Acliad/Ahsokas-Lightsaber/Reference Images/View 2.png

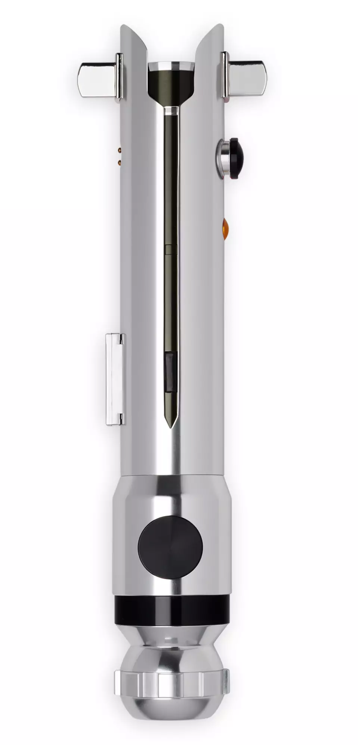
Reference Images/View 2.png
