Acliad/Ahsokas-Lightsaber/Mechanical/Meshes/Wing.stl

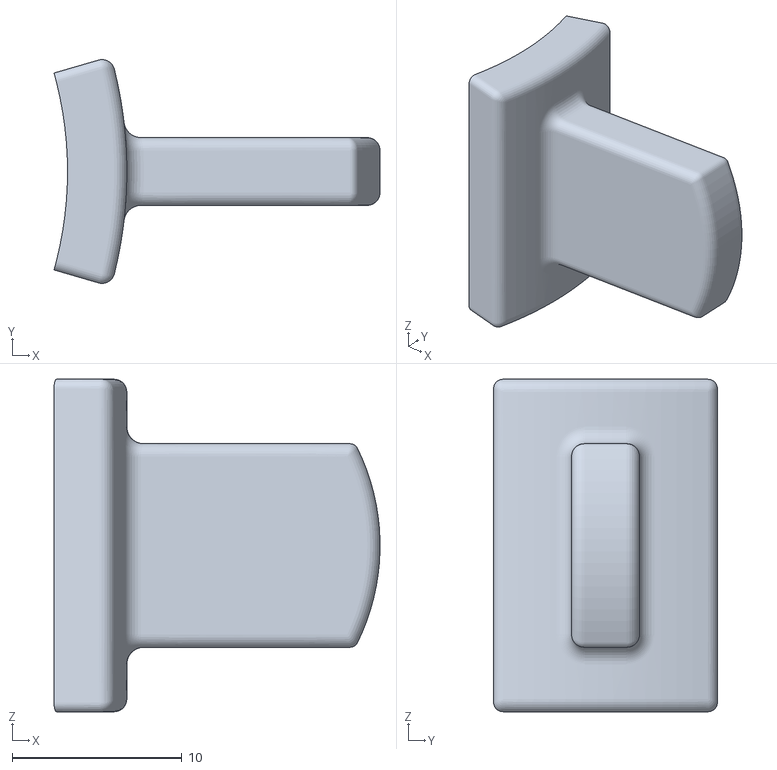
[picture p18: CAD file, 2024-09-22]
Mechanical/Meshes/Wing.stl
19.2 x 13.2 x 19.6
