Acliad/Ahsokas-Lightsaber/Mechanical/Meshes/Power Button Cap.stl

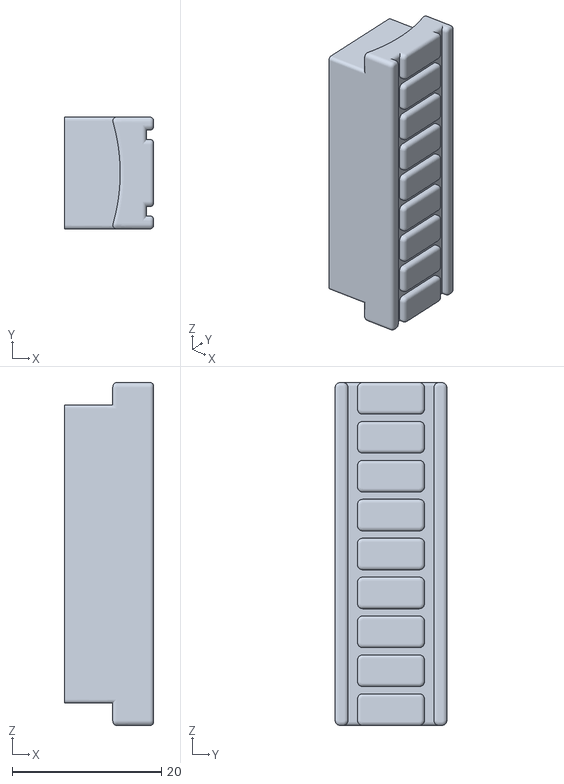
[picture p19: CAD file, 2024-09-22]
Mechanical/Meshes/Power Button Cap.stl
12.0 x 15.0 x 46.0
