Acliad/Ahsokas-Lightsaber/Mechanical/Solids/Carrier.stp

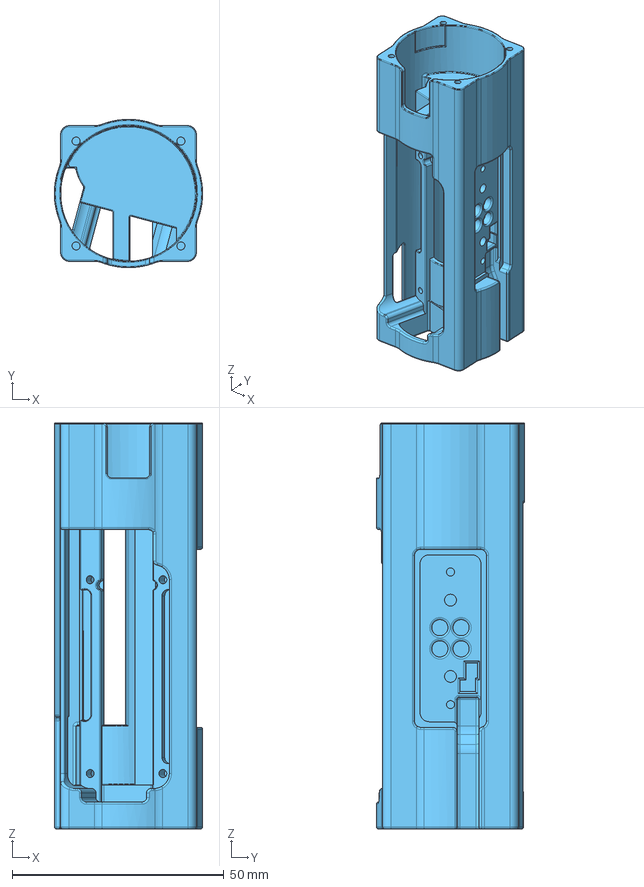
[picture p20: CAD file, 2024-09-22]
Mechanical/Solids/Carrier.stp
35.0 x 35.0 x 95.8 mm
