Acliad/Ahsokas-Lightsaber/Mechanical/Meshes/LED Strip Keeper.stl

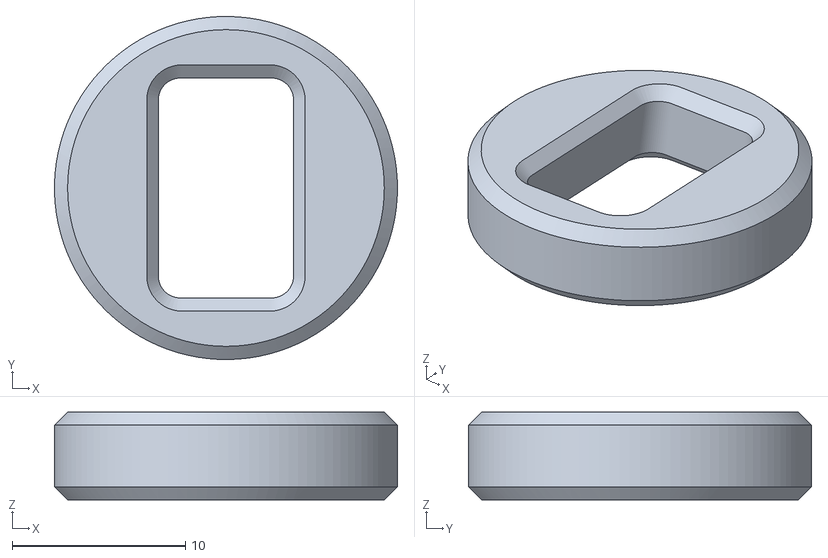
[picture p21: CAD file, 2024-09-22]
Mechanical/Meshes/LED Strip Keeper.stl
19.8 x 19.8 x 5.08
